Aqanta/KeyJam/Design/3D Models/Knobs/Knob #6.stl

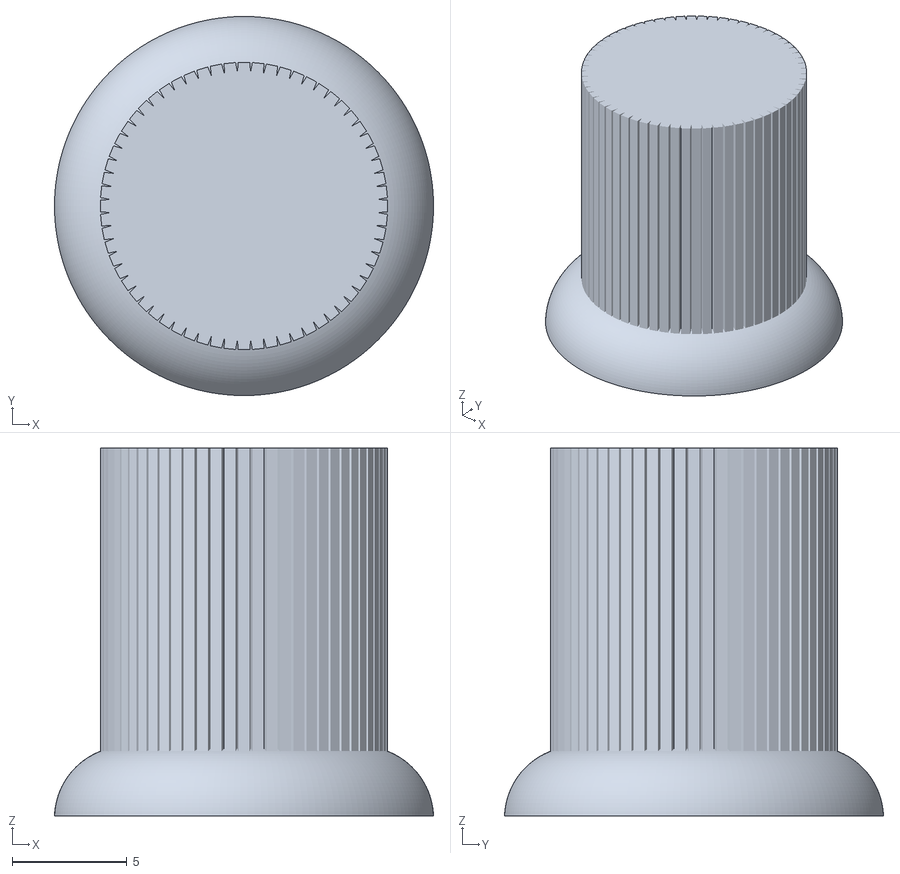
[picture p15: CAD file, 2024-03-14]
Design/3D Models/Knobs/Knob #6.stl
16.5 x 16.5 x 16.0
