Aqanta/KeyJam/Design/3D Models/Knobs/v1/Knob #6.stl

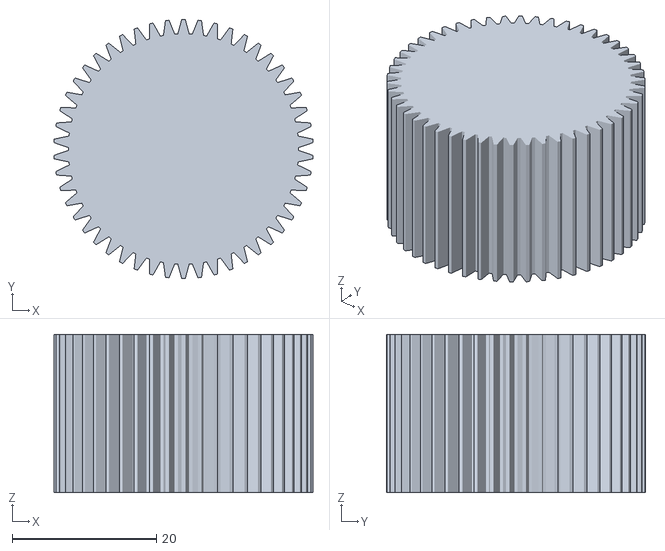
[picture p16: CAD file, 2024-03-09]
Design/3D Models/Knobs/v1/Knob #6.stl
36.0 x 36.0 x 22.0
