Aqanta/KeyJam/Design/3D Models/Sliders/Slider #1.stl

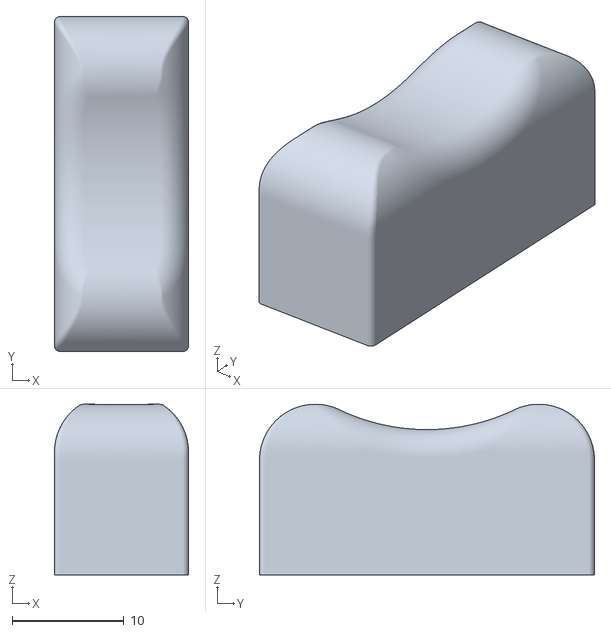
[picture p17: CAD file, 2024-03-14]
Design/3D Models/Sliders/Slider #1.stl
12.0 x 30.0 x 15.3
