Aqanta/KeyJam/Design/3D Models/Frames/KeyJam Bottom.stl

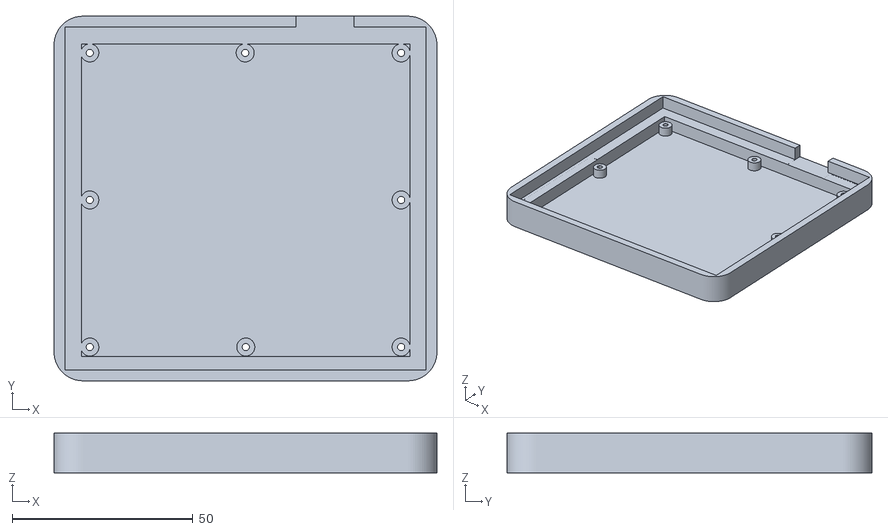
[picture p18: CAD file, 2024-03-17]
Design/3D Models/Frames/KeyJam Bottom.stl
106.1 x 101.0 x 11.0
