Aqanta/KeyJam/Design/3D Models/Keycap Prototypes/flat_square.stl

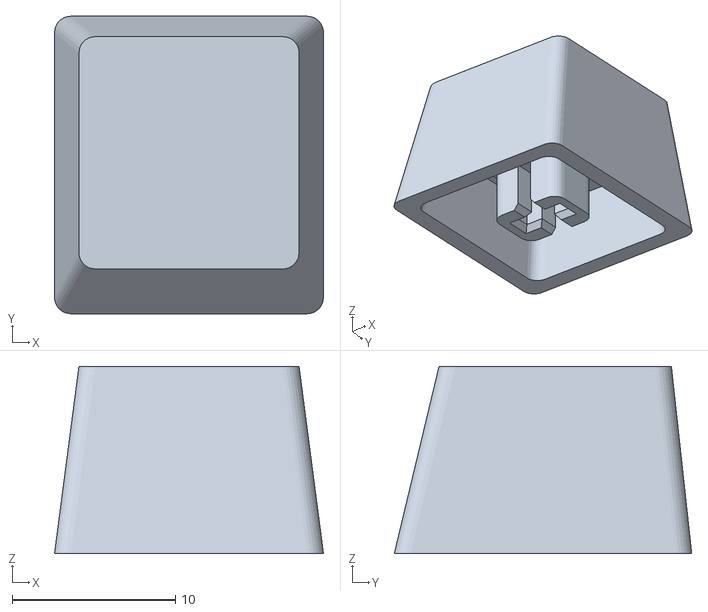
[picture p19: CAD file, 2024-02-24]
Design/3D Models/Keycap Prototypes/flat_square.stl
16.5 x 18.2 x 11.5
