Aqanta/KeyJam/Design/3D Models/Knobs/Knob #3.stl

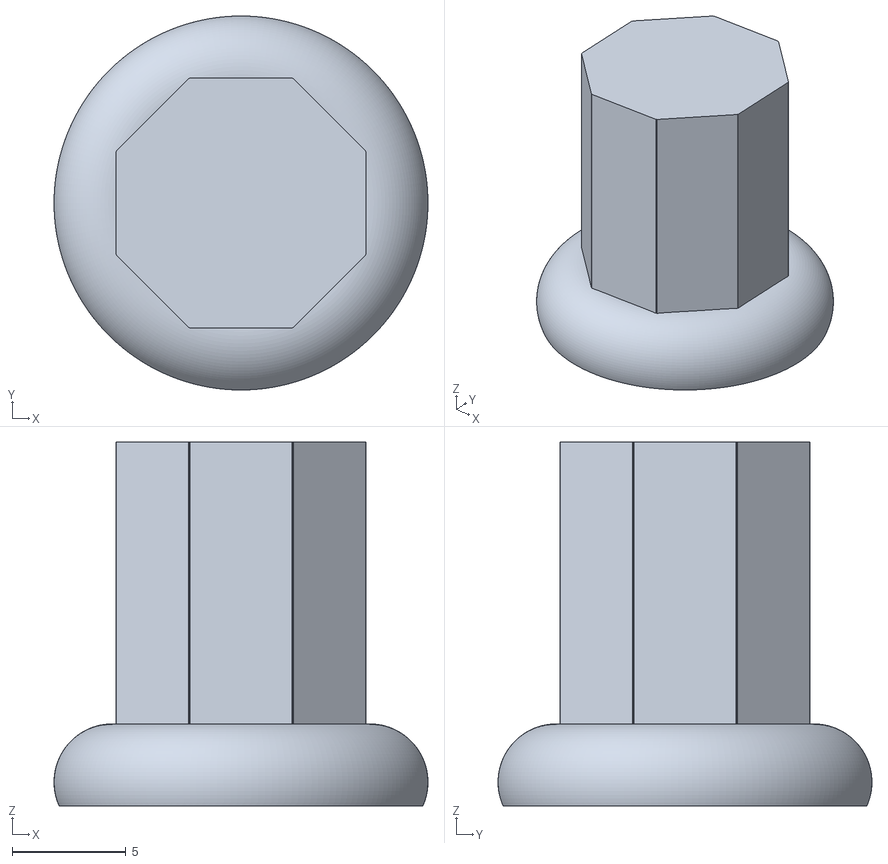
[picture p20: CAD file, 2024-03-14]
Design/3D Models/Knobs/Knob #3.stl
16.4 x 16.4 x 16.0
