Aqanta/KeyJam/Design/3D Models/Knobs/v1/Knob #4.stl

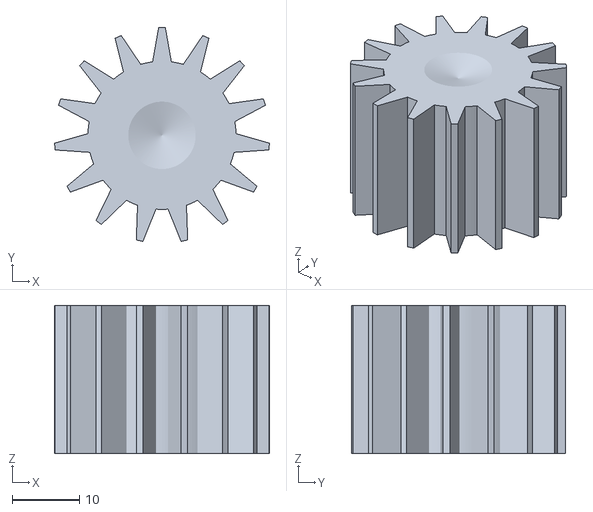
[picture p21: CAD file, 2024-03-09]
Design/3D Models/Knobs/v1/Knob #4.stl
31.9 x 31.8 x 22.0
