Aqanta/KeyJam/Design/3D Models/Frames/KeyJam Max Tippity-Top.stl

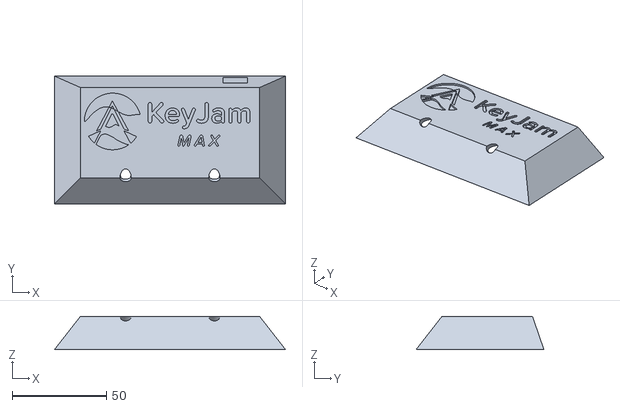
[picture p22: CAD file, 2024-03-14]
Design/3D Models/Frames/KeyJam Max Tippity-Top.stl
122.3 x 67.7 x 17.5
