Aqanta/KeyJam/Design/3D Models/Keycap Prototypes/dsa_key.stl

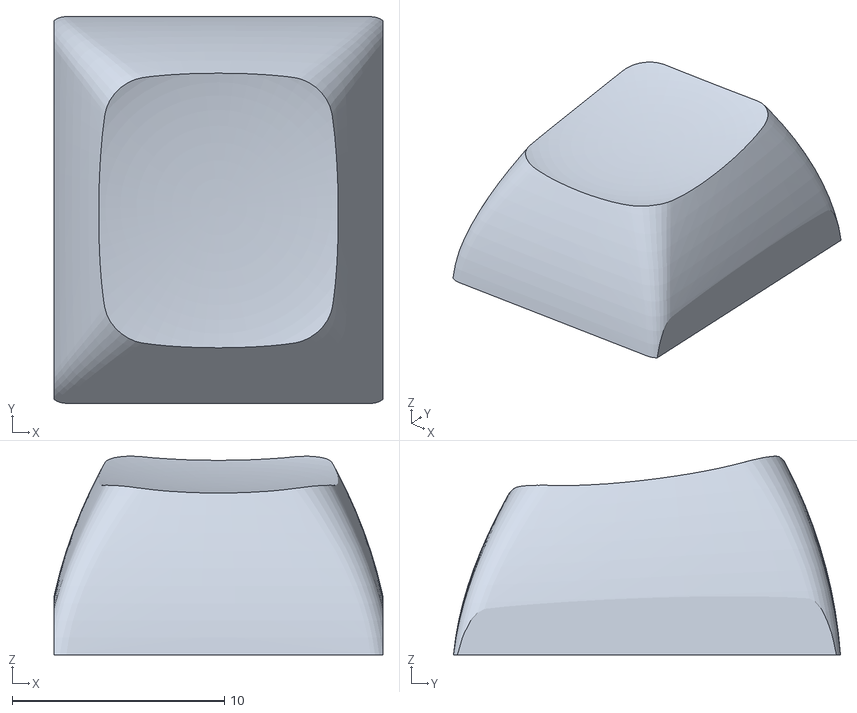
[picture p23: CAD file, 2024-02-24]
Design/3D Models/Keycap Prototypes/dsa_key.stl
15.5 x 18.2 x 9.36
