Aqanta/KeyJam/Design/3D Models/Knobs/Knob #2.stl

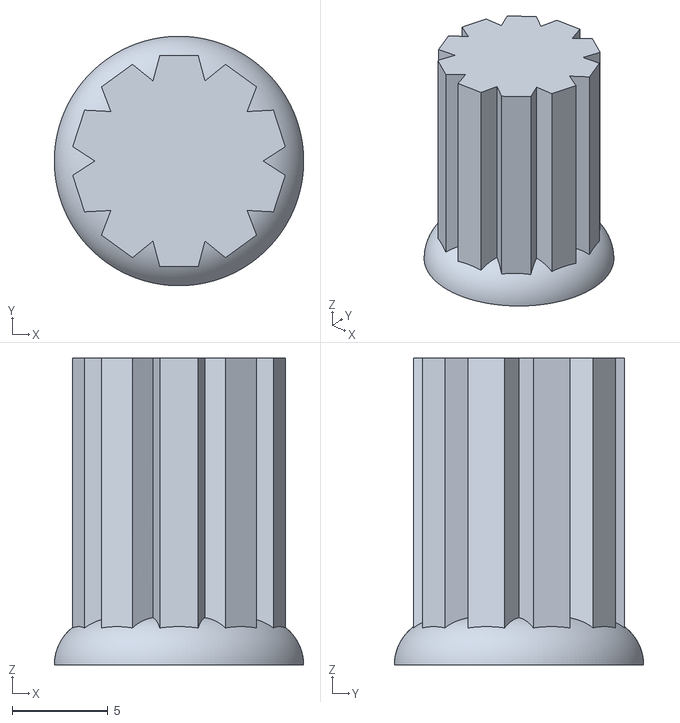
[picture p24: CAD file, 2024-03-14]
Design/3D Models/Knobs/Knob #2.stl
13.0 x 13.0 x 16.0
