Aqanta/KeyJam/Design/3D Models/Knobs/v1/Knob #2.stl

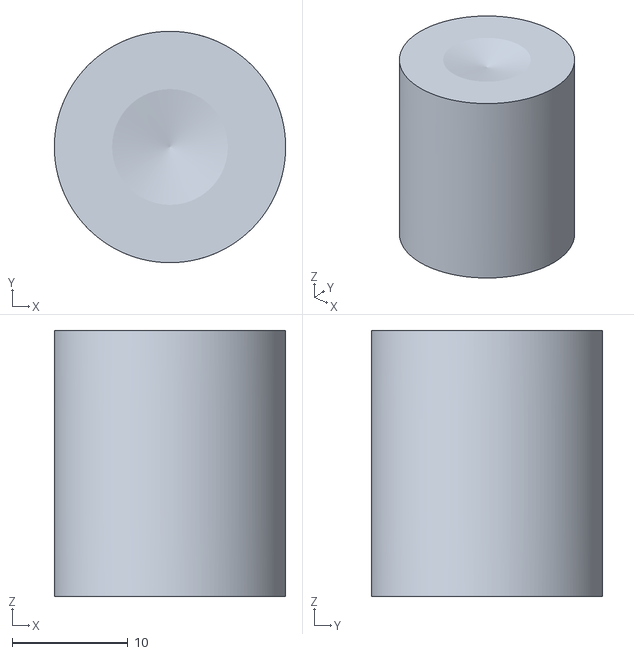
[picture p25: CAD file, 2024-03-09]
Design/3D Models/Knobs/v1/Knob #2.stl
20.0 x 20.0 x 23.0
