Aqanta/KeyJam/Design/3D Models/Frames/KeyJam Max Frame.stl

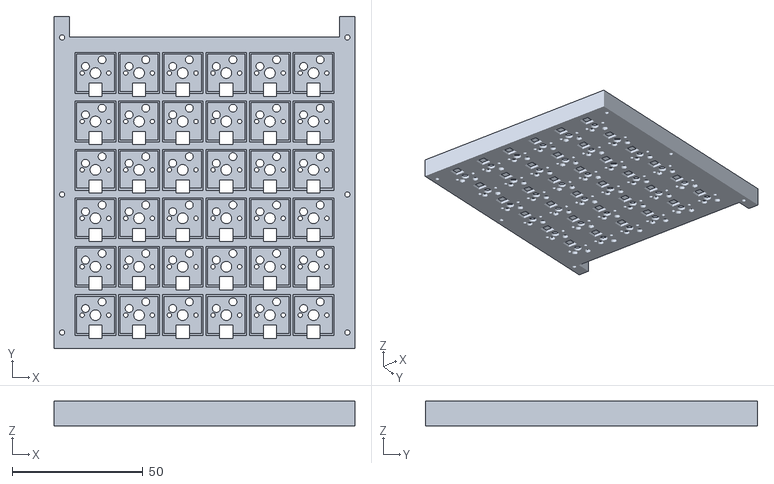
[picture p26: CAD file, 2024-03-14]
Design/3D Models/Frames/KeyJam Max Frame.stl
115.0 x 126.9 x 9.50
