Aqanta/KeyJam/Design/3D Models/Keycap Prototypes/g20_key.stl

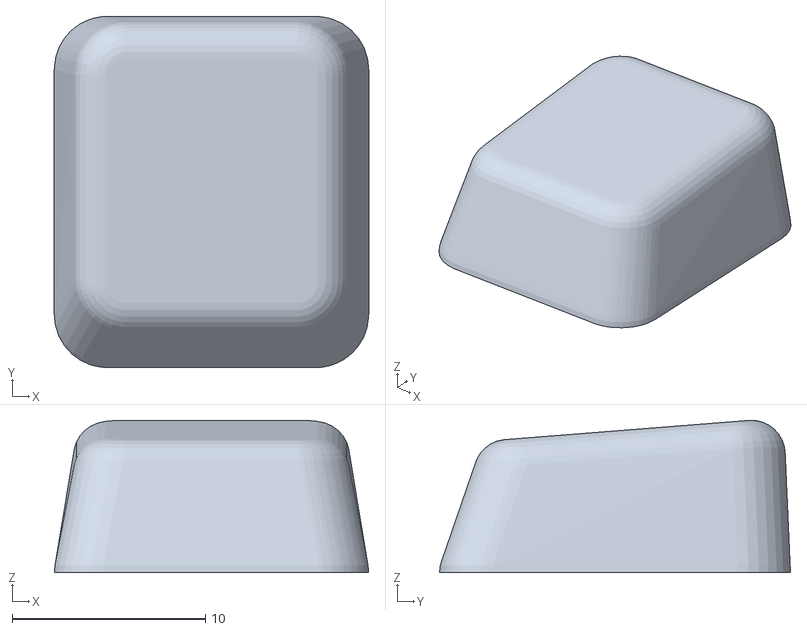
[picture p27: CAD file, 2024-02-24]
Design/3D Models/Keycap Prototypes/g20_key.stl
16.3 x 18.1 x 7.86
