Aqanta/KeyJam/Design/3D Models/Knobs/Knob #4.stl

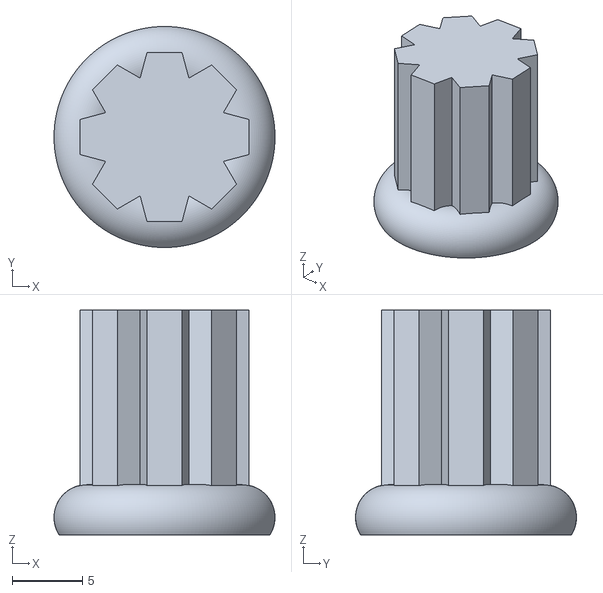
[picture p28: CAD file, 2024-03-14]
Design/3D Models/Knobs/Knob #4.stl
15.7 x 15.7 x 16.0
