Aqanta/KeyJam/Design/3D Models/Knobs/v1/Knob #3.stl

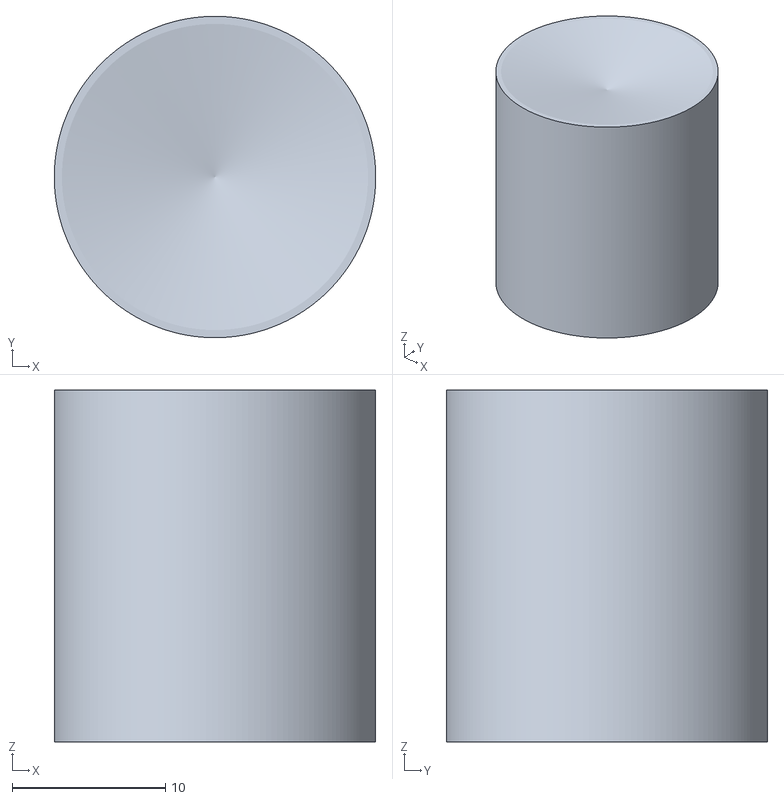
[picture p29: CAD file, 2024-03-09]
Design/3D Models/Knobs/v1/Knob #3.stl
21.0 x 21.0 x 23.0
