Aqanta/KeyJam/Design/3D Models/Frames/KeyJam Key Frame.stl

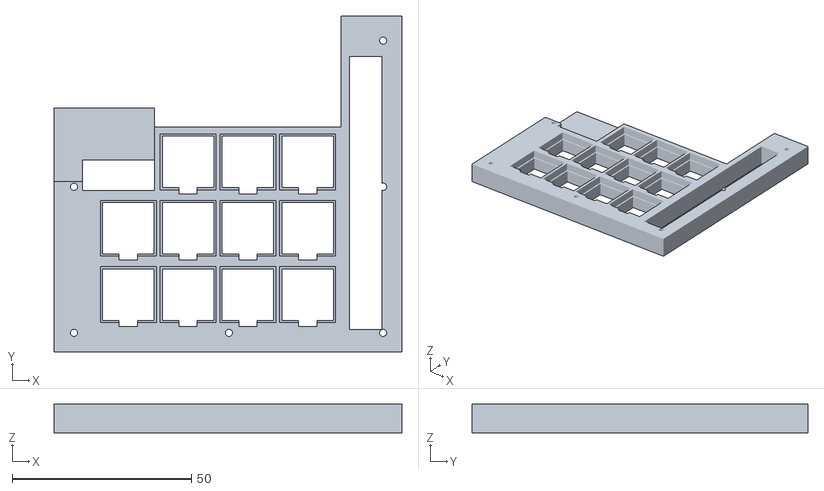
[picture p30: CAD file, 2024-03-10]
Design/3D Models/Frames/KeyJam Key Frame.stl
97.0 x 93.7 x 8.00
